AdrianMagallon/ESP-Rover/Hardware/Esp-rover.kicad_sch

## KiCad design Hardware/Esp-rover.kicad_sch (2026-08-16)

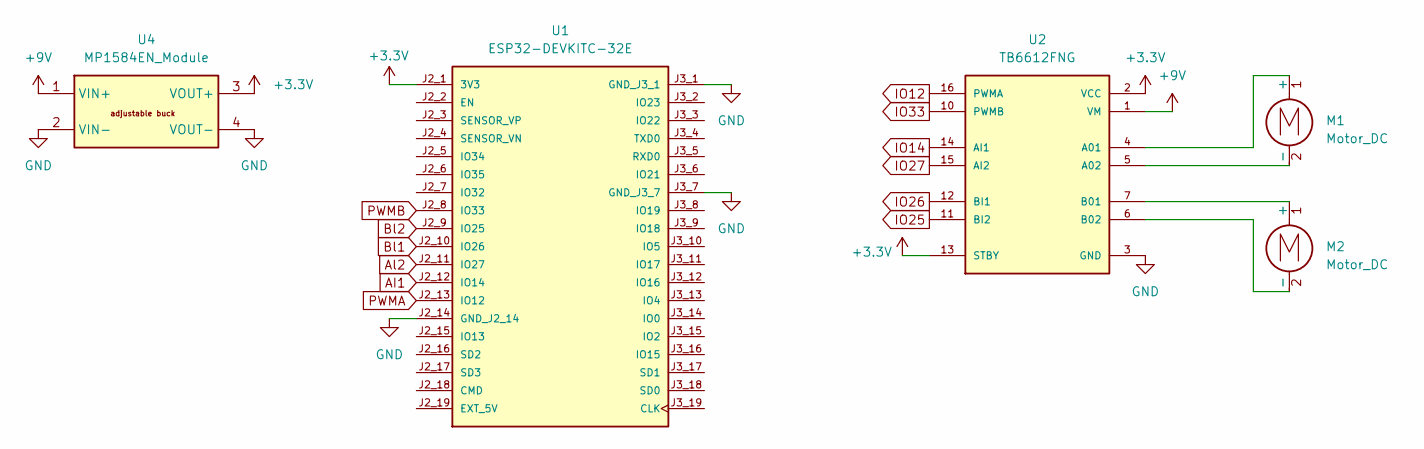
[picture p2: schematic Esp-rover.kicad_sch]

Parts:
M1, M2: Motor_DC
U1: ESP32-DEVKITC-32E; MODULE_ESP32-DEVKITC-32E; PARTREV 1.4
U2: TB6612FNG; MODULE_ROB-14450; PARTREV 11-13-17
U4: MP1584EN_Module

Connections:
+3.3V: U1.J2_1 (3V3), U2.2 (VCC), U2.13 (STBY), U4.3 (VOUT+)
+9V: U2.1 (VM), U4.1 (VIN+)
AI1: U1.J2_12 (IO14)
Al2: U1.J2_11 (IO27)
Bl1: U1.J2_10 (IO26)
Bl2: U1.J2_9 (IO25)
GND: U1.J2_14 (GND_J2_14), U1.J3_1 (GND_J3_1), U1.J3_7 (GND_J3_7), U2.3 (GND), U2.8 (GND), U2.9 (GND), U4.2 (VIN-), U4.4 (VOUT-)
IO12: U2.16 (PWMA)
IO14: U2.14 (AI1)
IO25: U2.11 (BI2)
IO26: U2.12 (BI1)
IO27: U2.15 (AI2)
IO33: U2.10 (PWMB)
unnamed: M1.1 (+), U2.4 (A01)
unnamed: M1.2 (-), U2.5 (A02)
unnamed: M2.1 (+), U2.7 (B01)
unnamed: M2.2 (-), U2.6 (B02)
PWMA: U1.J2_13 (IO12)
PWMB: U1.J2_8 (IO33)
